CyberPit/FreeDSP-FreeUSBi_Programmer_hybrid_version/Photo/FreeUSBi_0V51_BOTTOM.jpg

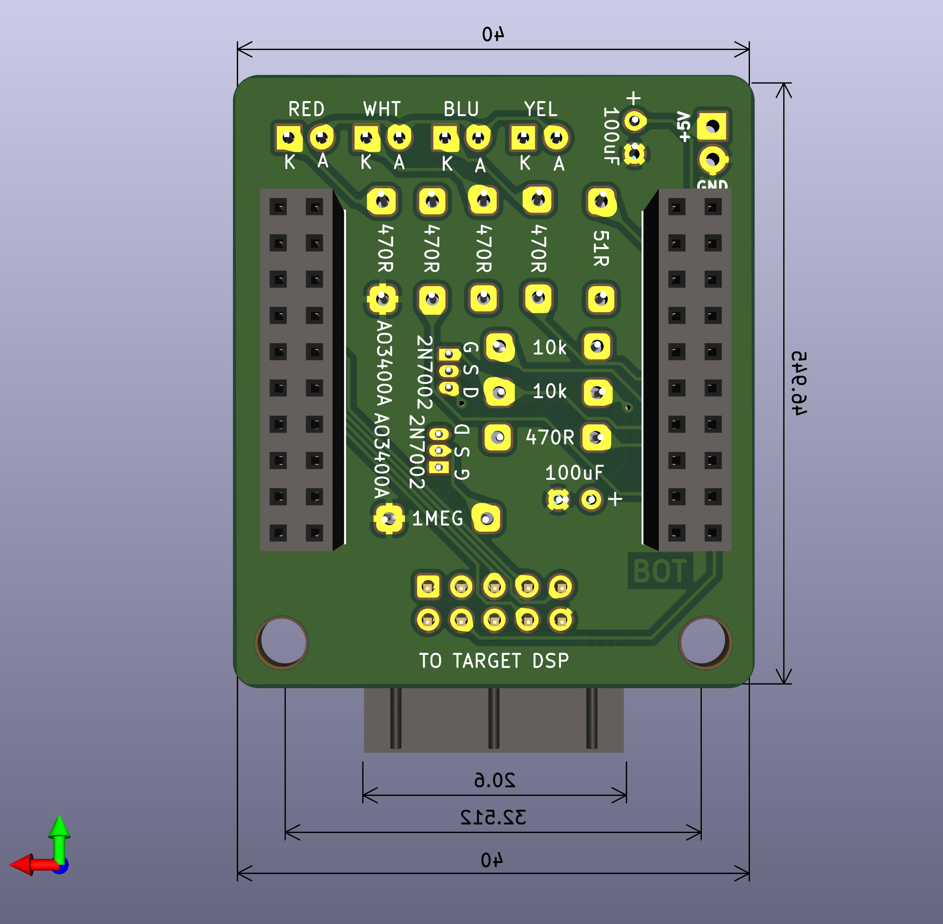
Photo/FreeUSBi_0V51_BOTTOM.jpg
