CyberPit/FreeDSP-FreeUSBi_Programmer_hybrid_version/Photo/FreeUSBi_Programmer0v3.jpg

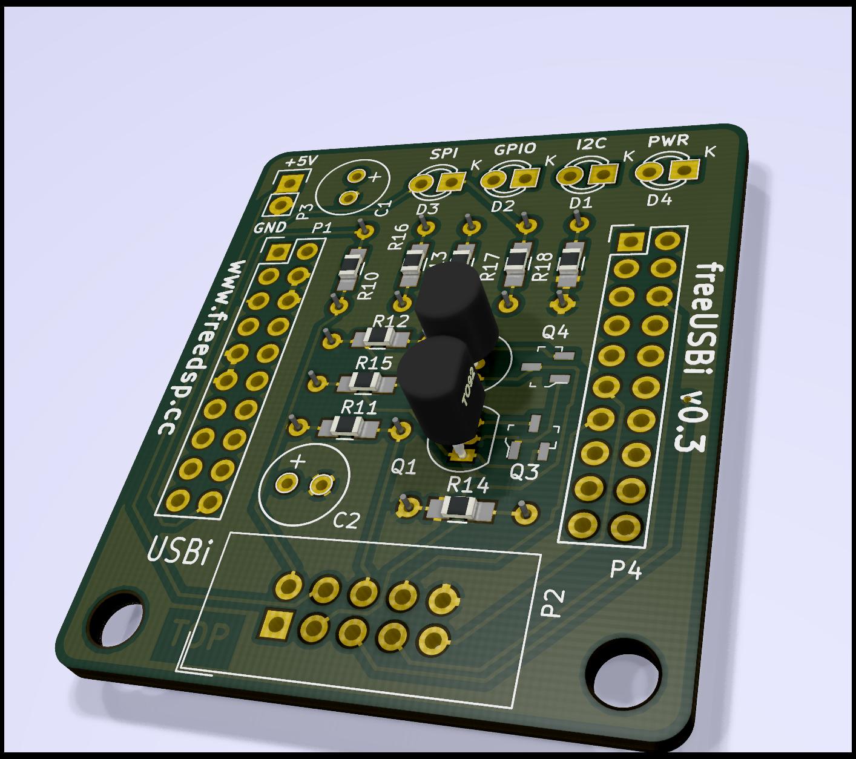
Photo/FreeUSBi_Programmer0v3.jpg
